mpainenz/led-terrarium-pi/assets/img/20160203_145956.jpg

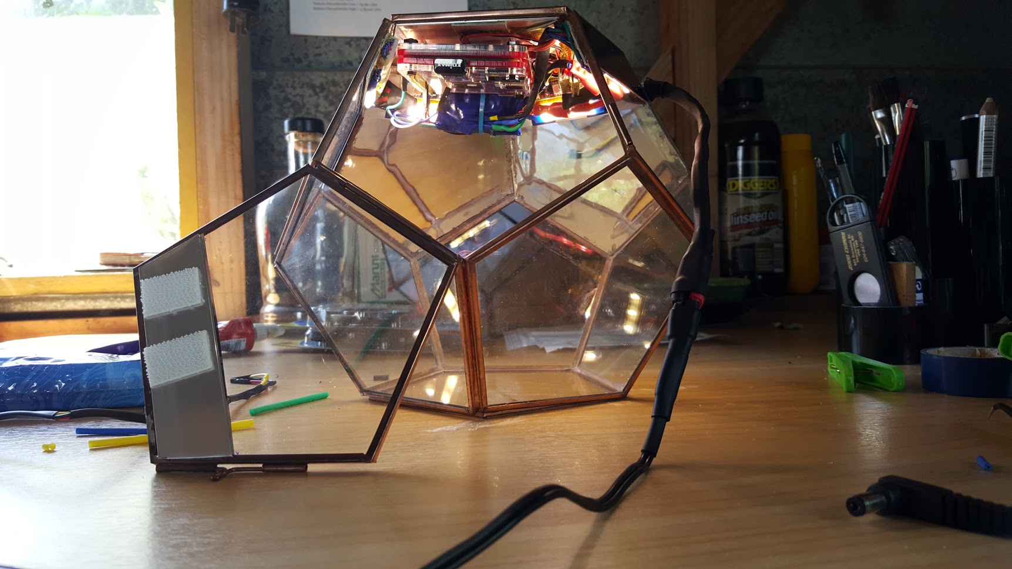
assets/img/20160203_145956.jpg
