mpainenz/led-terrarium-pi/assets/img/20160320_183034.jpg

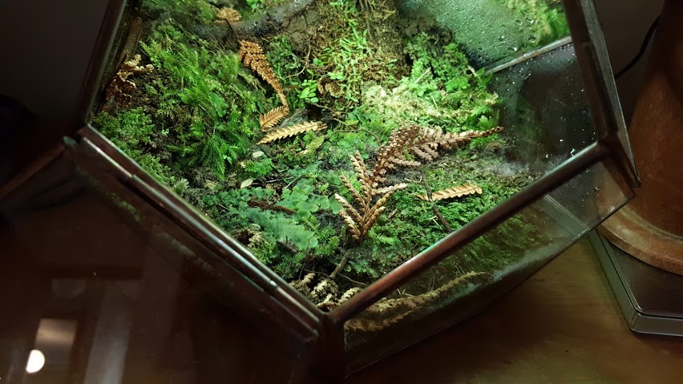
assets/img/20160320_183034.jpg
