mpainenz/led-terrarium-pi/assets/img/DSC00021.JPG

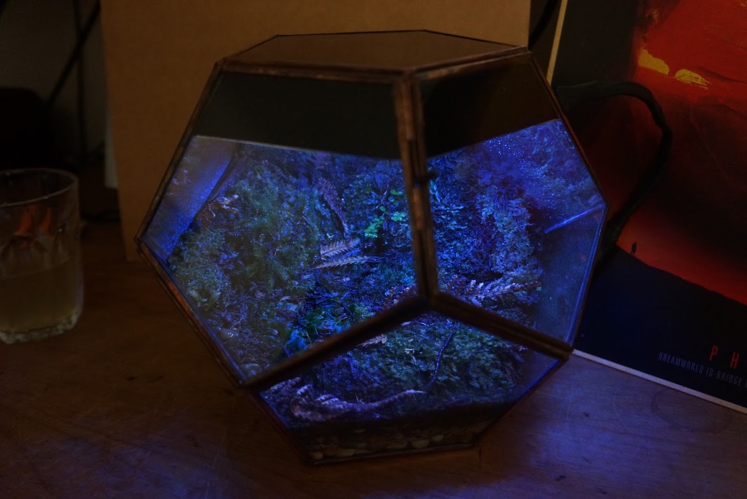
assets/img/DSC00021.JPG
