mpainenz/led-terrarium-pi/assets/img/header/Header.png

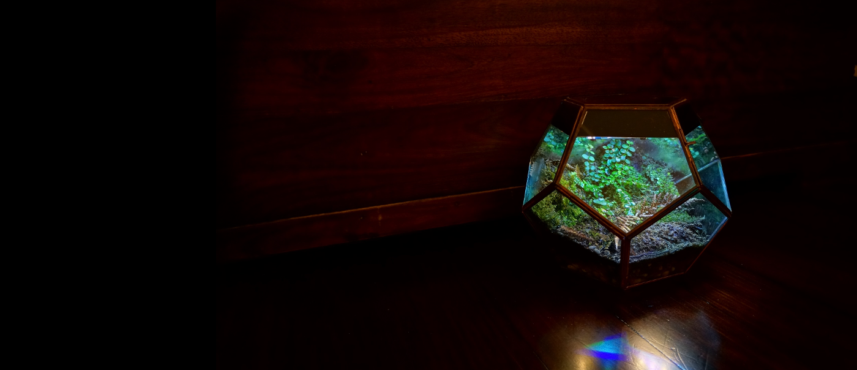
assets/img/header/Header.png
